codinghead/touchshield/documentation/SPI-transfer-1.png

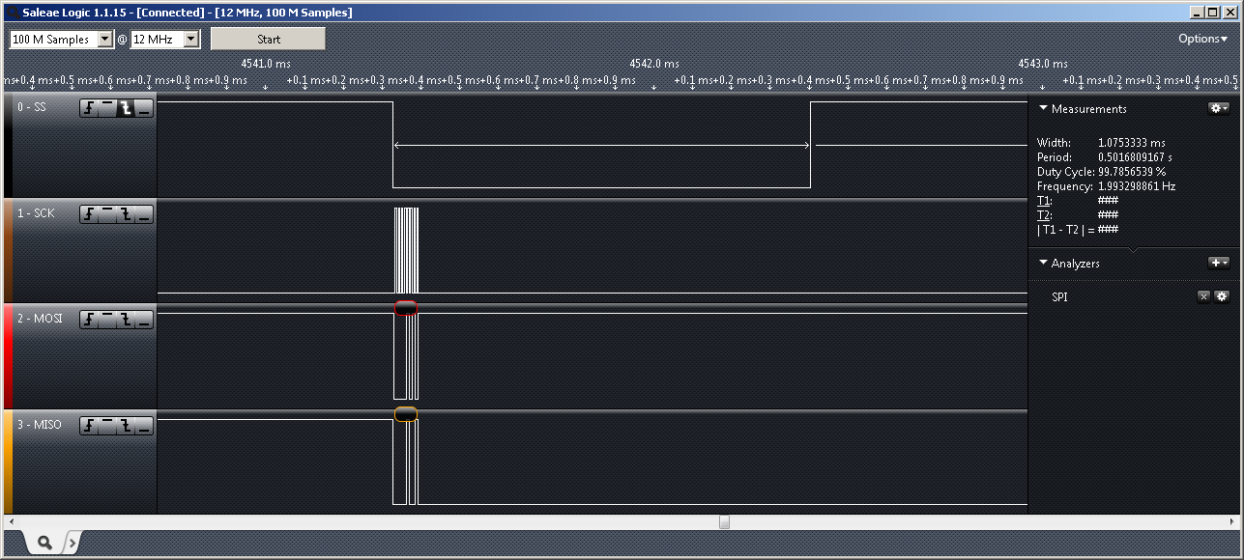
documentation/SPI-transfer-1.png
