codinghead/touchshield/documentation/SPI-transfer-2.png

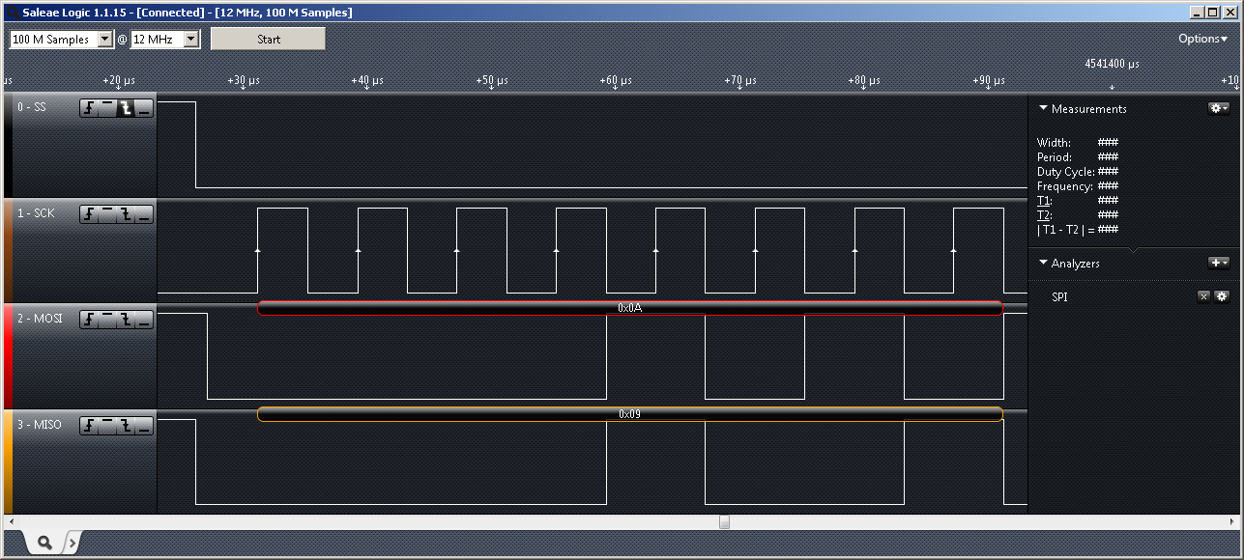
documentation/SPI-transfer-2.png
