codinghead/touchshield/documentation/SPI-transfer-3-SS-Rises-Too-Early.png

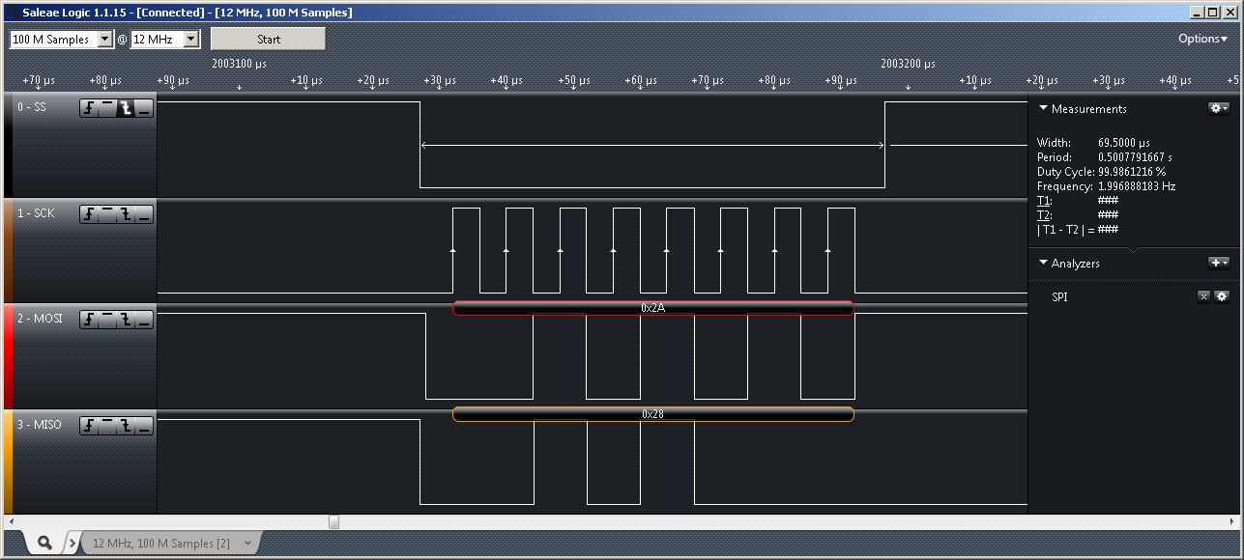
documentation/SPI-transfer-3-SS-Rises-Too-Early.png
