codinghead/touchshield/documentation/SPI-transfer-4-SS-Rises-Too-Early.png

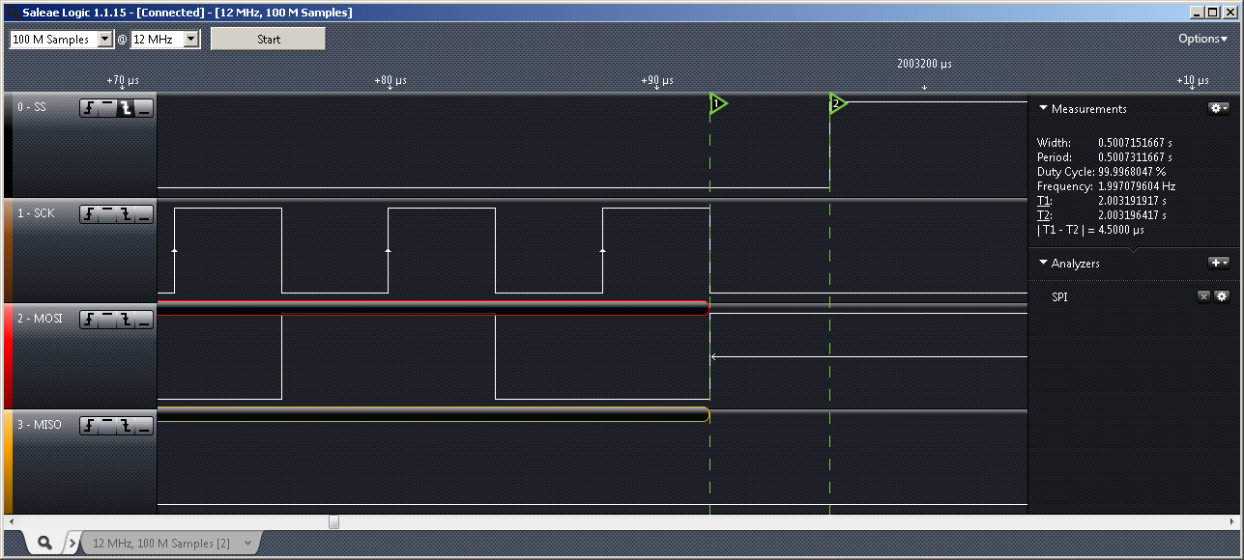
documentation/SPI-transfer-4-SS-Rises-Too-Early.png
