codinghead/touchshield/documentation/SPI-transfer-5-5-byte-packets-full-speed.png

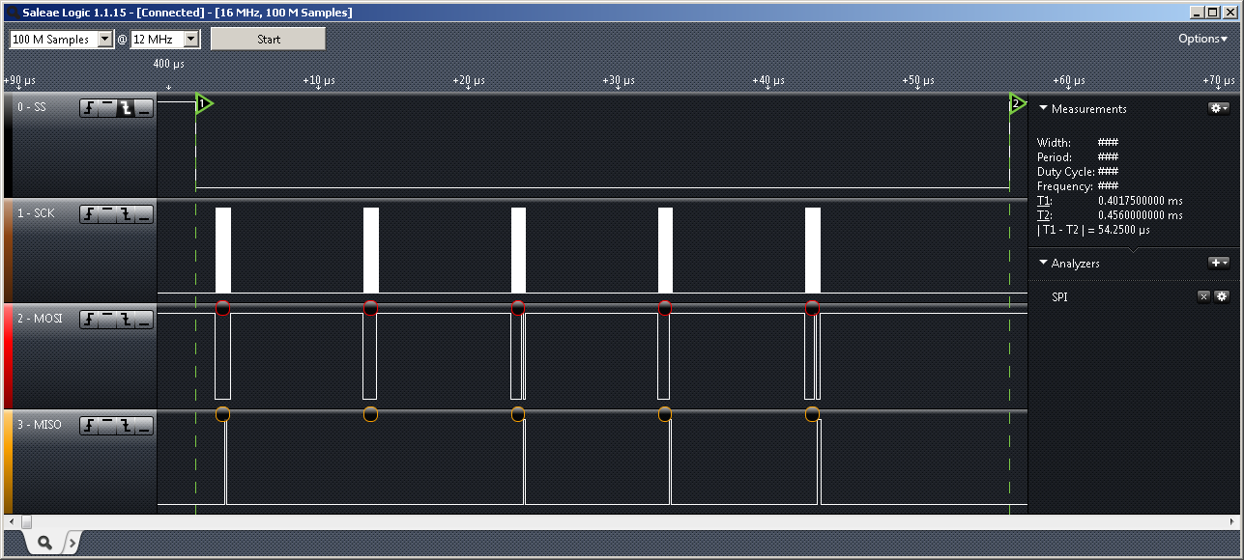
documentation/SPI-transfer-5-5-byte-packets-full-speed.png
