codinghead/touchshield/documentation/SPI-transfer-6-5-byte-packets-first-transfer.png

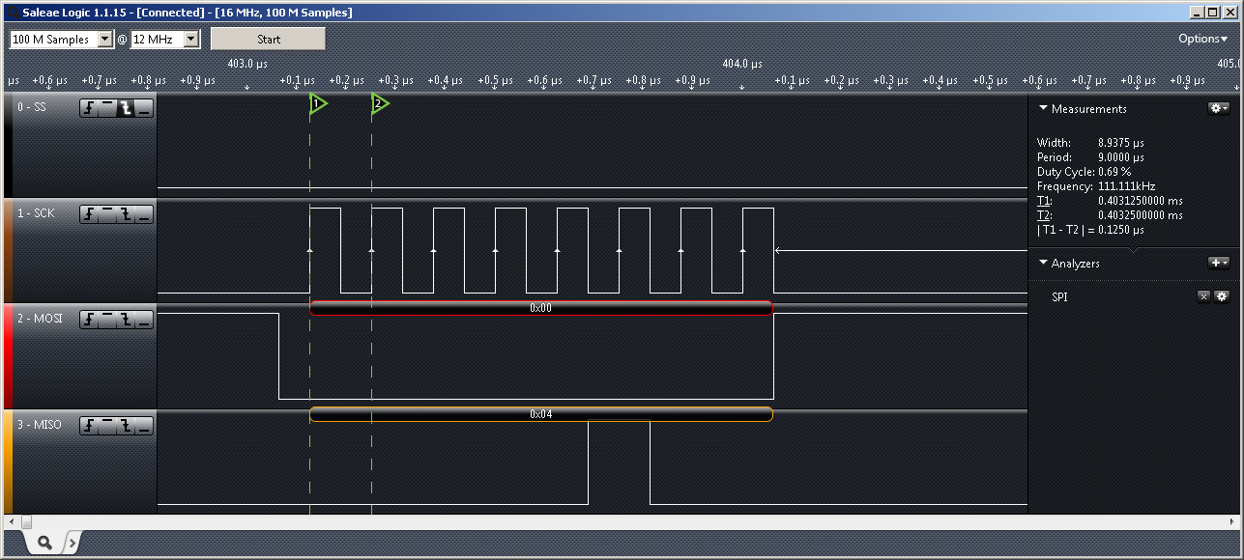
documentation/SPI-transfer-6-5-byte-packets-first-transfer.png
