codinghead/touchshield/documentation/SPI-transfer-7-5-byte-packets-SS-fall-edge-to-first-CLK.png

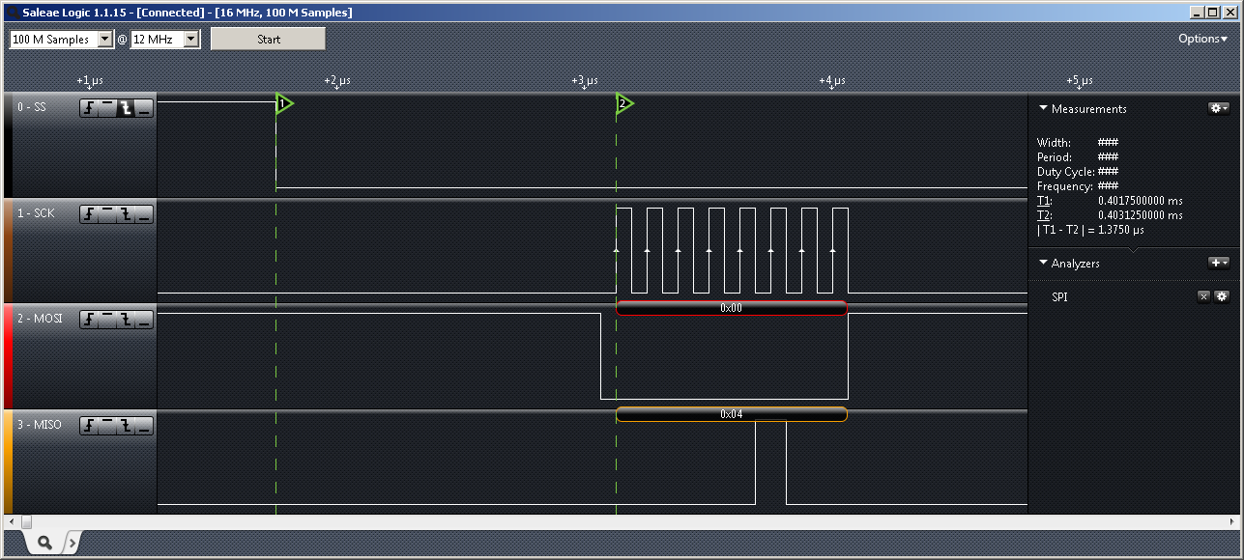
documentation/SPI-transfer-7-5-byte-packets-SS-fall-edge-to-first-CLK.png
