codinghead/touchshield/documentation/SPI-transfer-8-5-byte-packets-last-CLK-to-SS-rising-edge.png

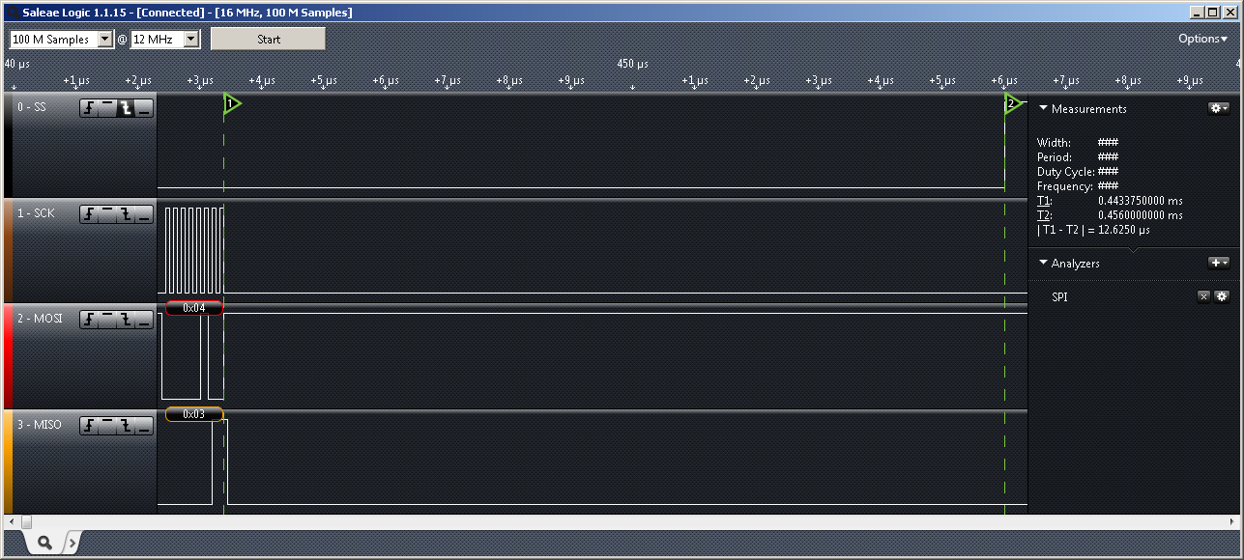
documentation/SPI-transfer-8-5-byte-packets-last-CLK-to-SS-rising-edge.png
