codinghead/touchshield/images/by-sa.bmp

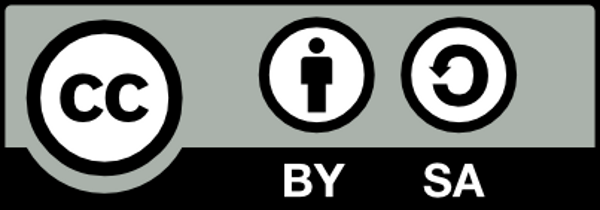
images/by-sa.bmp
