codinghead/touchshield/images/MultiTouch-Interface_Mouse-theme_1-finger-Simple-Tap.png

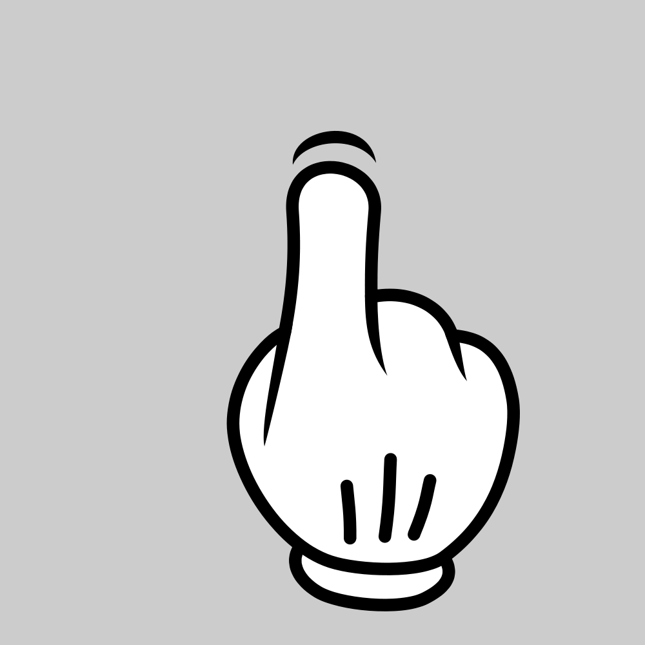
images/MultiTouch-Interface_Mouse-theme_1-finger-Simple-Tap.png
