codinghead/touchshield/images/QTouchShieldRender2.png

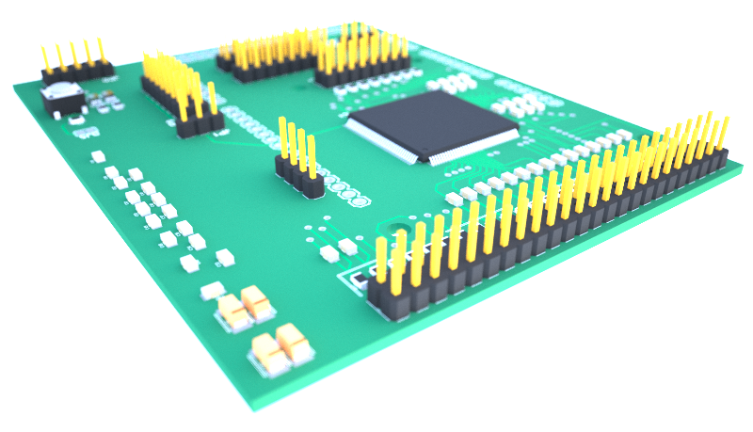
images/QTouchShieldRender2.png
