codinghead/touchshield/software/uc3c0512c/UC3C-Test/UC3C-Test/src/config/conf_board.h

/**
 * \file
 *
 * \brief User board configuration template
 *
 */

#ifndef CONF_BOARD_H
#define CONF_BOARD_H

// External oscillator settings.
// Uncomment and set correct values if external oscillator is used.

// External oscillator frequency
//#define BOARD_XOSC_HZ          8000000

// External oscillator type.
//!< External clock signal
//#define BOARD_XOSC_TYPE        XOSC_TYPE_EXTERNAL
//!< 32.768 kHz resonator on TOSC
//#define BOARD_XOSC_TYPE        XOSC_TYPE_32KHZ
//!< 0.4 to 16 MHz resonator on XTALS
//#define BOARD_XOSC_TYPE        XOSC_TYPE_XTAL

// External oscillator startup time
//#define BOARD_XOSC_STARTUP_US  500000

// Define SPI0 interface on PORTD
#define SPI0_SS         AVR32_PIN_PD03
#define SPI0_MOSI       AVR32_PIN_PD04
#define SPI0_MISO       AVR32_PIN_PD05
#define SPI0_SCK        AVR32_PIN_PD06

#endif // CONF_BOARD_H
