codinghead/touchshield/software/uc3c0512c/UC3C-Test/UC3C-Test/src/asf/avr32/drivers/scif/scif_uc3c.c

/*****************************************************************************
 *
 * \file
 *
 * \brief System Control InterFace(SCIF) driver.
 *
 * Copyright (c) 2009 Atmel Corporation. All rights reserved.
 *
 * \asf_license_start
 *
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
 * 3. The name of Atmel may not be used to endorse or promote products derived
 *    from this software without specific prior written permission.
 *
 * 4. This software may only be redistributed and used in connection with an
 *    Atmel microcontroller product.
 *
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
 * \asf_license_stop
 *
 *****************************************************************************/


#include "compiler.h"
#include "scif_uc3c.h"


/*! \name SCIF Writable Bit-Field Registers
 */
//! @{

typedef union
{
  unsigned long                 oscctrl[2];
  avr32_scif_oscctrl_t          OSCCTRL[2];
} u_avr32_scif_oscctrl_t;

typedef union
{
  unsigned long                 pll[2];
  avr32_scif_pll_t              PLL[2];
} u_avr32_scif_pll_t;

typedef union
{
  unsigned long                 oscctrl32;
  avr32_scif_oscctrl32_t         OSCCTRL32;
} u_avr32_scif_oscctrl32_t;



//! @}


//----- PRIVATE FUNCTIONS

/*! \brief Wait for a status high in the Power and Clocks status register.
 *
 * \param statusMask Mask field of the status to poll [INPUT]
 *
 * \return Status.
 *   \retval 0   Status is high.
 *   \retval <0  SCIF_POLL_TIMEOUT Timeout expired before the status was high.
 */
static long int scif_pclksr_statushigh_wait(unsigned long statusMask)
{
  unsigned int  timeout = SCIF_POLL_TIMEOUT;

  while(!(AVR32_SCIF.pclksr & statusMask))
  {
    if(--timeout == 0)
      return -1;
  }
  return PASS;
}

unsigned long scif_read_gplp(unsigned long gplp)
{
  return AVR32_SCIF.gplp[gplp];
}


void scif_write_gplp(int gplp, unsigned long value)
{
  SCIF_UNLOCK(AVR32_SCIF_GPLP + 4*gplp);
  AVR32_SCIF.gplp[gplp] = value;
}

/**
 ** Interrupt Functions
 **/
// Implemented as inline in scif_uc3x.h


/**
 ** Power and Clocks Status Functions
 **/
// Implemented as inline in scif_uc3x.h


/**
 ** OSC0/OSC1 Functions
 **/

long int scif_start_osc(scif_osc_t osc, const scif_osc_opt_t *opt, bool wait_for_ready)
{
  u_avr32_scif_oscctrl_t   u_avr32_scif_oscctrl;

#ifdef AVR32SFW_INPUT_CHECK
  // Check that the input frequency is in the supported frequency range.
  if( (opt->freq_hz < SCIF_EXT_CRYSTAL_MIN_FREQ_HZ)
      || (opt->freq_hz > SCIF_EXT_CRYSTAL_MAX_FREQ_HZ))
  {
    return -1;
  }
  // Check : for OSC0/OSC1, only 2 modes are supported
  if( (opt->mode != SCIF_OSC_MODE_EXT_CLK)
      && (opt->mode != SCIF_OSC_MODE_2PIN_CRYSTAL))
  {
    return -1;
  }

  if (osc == SCIF_OSC0)
  {
    // Check that the startup value is in the supported range.
    if(opt->startup > (unsigned char)AVR32_SCIF_OSCCTRL0_STARTUP_16384_RCOSC)
    {
      return -1;
    }
    // Check that the gain value is in the supported range.
    if(opt->gain > AVR32_SCIF_OSCCTRL0_GAIN_G3)
    {
      return -1;
    }
  }
  else
  {
    // Check that the startup value is in the supported range.
    if(opt->startup > (unsigned char)AVR32_SCIF_OSCCTRL1_STARTUP_16384_RCOSC)
    {
      return -1;
    }
    // Check that the gain value is in the supported range.
    if(opt->gain > AVR32_SCIF_OSCCTRL1_GAIN_G3)
    {
      return -1;
    }
  }
#endif  // AVR32SFW_INPUT_CHECK
  // Read Register
  u_avr32_scif_oscctrl.OSCCTRL[osc] = AVR32_SCIF.OSCCTRL[osc] ;
  // Modify: Configure & start OSC0.
  u_avr32_scif_oscctrl.OSCCTRL[osc].mode = opt->mode;
  u_avr32_scif_oscctrl.OSCCTRL[osc].gain = opt->gain;
  u_avr32_scif_oscctrl.OSCCTRL[osc].startup = opt->startup;
  u_avr32_scif_oscctrl.OSCCTRL[osc].oscen = ENABLE;
  AVR32_ENTER_CRITICAL_REGION( );
  // Unlock the write-protected OSCCTRL0 register
  SCIF_UNLOCK(AVR32_SCIF_OSCCTRL + 4*osc);
  // Write Back
  AVR32_SCIF.OSCCTRL[osc] = u_avr32_scif_oscctrl.OSCCTRL[osc];
  AVR32_LEAVE_CRITICAL_REGION( );

  if(true == wait_for_ready)
  {
    // Wait until OSC0 is stable and ready to be used.
    if(scif_pclksr_statushigh_wait(AVR32_SCIF_PCLKSR_OSC0RDY_MASK))
      return -1;
  }
  return PASS;
}


bool scif_is_osc_ready(scif_osc_t osc)
{
  if (osc == SCIF_OSC0)
  {
    return((AVR32_SCIF.pclksr & AVR32_SCIF_PCLKSR_OSC0RDY_MASK)>>AVR32_SCIF_PCLKSR_OSC0RDY_OFFSET);
  }
  else
  {
    return((AVR32_SCIF.pclksr & AVR32_SCIF_PCLKSR_OSC1RDY_MASK)>>AVR32_SCIF_PCLKSR_OSC1RDY_OFFSET);
  }
}


long int scif_stop_osc(scif_osc_t osc)
{

  unsigned long temp;

  temp = AVR32_SCIF.oscctrl[osc];
  temp &= ~AVR32_SCIF_OSCCTRL_OSCEN_MASK;
  AVR32_ENTER_CRITICAL_REGION( );
  // Unlock the write-protected OSCCTRL0 register
  SCIF_UNLOCK(AVR32_SCIF_OSCCTRL + 4*osc);
  // Stop OSC0.
  AVR32_SCIF.oscctrl[osc] = temp;
  AVR32_LEAVE_CRITICAL_REGION( );

  return PASS;
}


long int scif_configure_osc_crystalmode(scif_osc_t osc, unsigned int fcrystal)
{
  u_avr32_scif_oscctrl_t   u_avr32_scif_oscctrl;

  if (osc == SCIF_OSC0)
  {
    // Read Register
    u_avr32_scif_oscctrl.OSCCTRL[SCIF_OSC0] = AVR32_SCIF.OSCCTRL[SCIF_OSC0] ;
    // Modify : Configure the oscillator mode to crystal and set the gain according to the
    // cyrstal frequency.
    u_avr32_scif_oscctrl.OSCCTRL[SCIF_OSC0].mode = SCIF_OSC_MODE_2PIN_CRYSTAL;
    u_avr32_scif_oscctrl.OSCCTRL[SCIF_OSC0].gain = (fcrystal <  900000) ? AVR32_SCIF_OSCCTRL0_GAIN_G0 :
                                                   (fcrystal < 3000000) ? AVR32_SCIF_OSCCTRL0_GAIN_G1 :
                                                   (fcrystal < 8000000) ? AVR32_SCIF_OSCCTRL0_GAIN_G2 :
                                                                          AVR32_SCIF_OSCCTRL0_GAIN_G3;
    AVR32_ENTER_CRITICAL_REGION( );
    // Unlock the write-protected OSCCTRL0 register
    SCIF_UNLOCK(AVR32_SCIF_OSCCTRL);
    // Write Back
    AVR32_SCIF.OSCCTRL[SCIF_OSC0] = u_avr32_scif_oscctrl.OSCCTRL[SCIF_OSC0];
    AVR32_LEAVE_CRITICAL_REGION( );
  }
  else
  {
    // Read Register
    u_avr32_scif_oscctrl.OSCCTRL[SCIF_OSC1] = AVR32_SCIF.OSCCTRL[SCIF_OSC1] ;
    // Modify : Configure the oscillator mode to crystal and set the gain according to the
    // cyrstal frequency.
    u_avr32_scif_oscctrl.OSCCTRL[SCIF_OSC1].mode = SCIF_OSC_MODE_2PIN_CRYSTAL;
    u_avr32_scif_oscctrl.OSCCTRL[SCIF_OSC1].gain = (fcrystal <  900000) ? AVR32_SCIF_OSCCTRL1_GAIN_G0 :
                                                   (fcrystal < 3000000) ? AVR32_SCIF_OSCCTRL1_GAIN_G1 :
                                                   (fcrystal < 8000000) ? AVR32_SCIF_OSCCTRL1_GAIN_G2 :
                                                                          AVR32_SCIF_OSCCTRL1_GAIN_G3;
    AVR32_ENTER_CRITICAL_REGION( );
    // Unlock the write-protected OSCCTRL1 register
    SCIF_UNLOCK(AVR32_SCIF_OSCCTRL + 4);
    // Write Back
    AVR32_SCIF.OSCCTRL[SCIF_OSC1] = u_avr32_scif_oscctrl.OSCCTRL[SCIF_OSC1];
    AVR32_LEAVE_CRITICAL_REGION( );
  }

  return PASS;
}

long int scif_configure_osc_extmode(scif_osc_t osc)
{
  u_avr32_scif_oscctrl_t   u_avr32_scif_oscctrl;

      // Read Register
    u_avr32_scif_oscctrl.OSCCTRL[osc] = AVR32_SCIF.OSCCTRL[osc] ;
    // Modify : Configure the oscillator mode to crystal and set the gain according to the
    // cyrstal frequency.
    u_avr32_scif_oscctrl.OSCCTRL[osc].mode = SCIF_OSC_MODE_EXT_CLK;
    AVR32_ENTER_CRITICAL_REGION( );
    // Unlock the write-protected OSCCTRL0 register
    SCIF_UNLOCK(AVR32_SCIF_OSCCTRL + 4*osc);
    // Write Back
    AVR32_SCIF.OSCCTRL[osc] = u_avr32_scif_oscctrl.OSCCTRL[osc];
    AVR32_LEAVE_CRITICAL_REGION( );

  return PASS;
}

long int scif_enable_osc(scif_osc_t osc, unsigned int startup, bool wait_for_ready)
{

  u_avr32_scif_oscctrl_t   u_avr32_scif_oscctrl;

  // Read Register
  u_avr32_scif_oscctrl.OSCCTRL[osc] = AVR32_SCIF.OSCCTRL[osc] ;
  // Modify: Configure the oscillator startup and enable the osc.
  u_avr32_scif_oscctrl.OSCCTRL[osc].startup = startup;
  u_avr32_scif_oscctrl.OSCCTRL[osc].oscen = ENABLE;
  AVR32_ENTER_CRITICAL_REGION( );
  // Unlock the write-protected OSCCTRL0 register
  SCIF_UNLOCK(AVR32_SCIF_OSCCTRL + 4*osc);
  // Write Back
  AVR32_SCIF.OSCCTRL[osc] = u_avr32_scif_oscctrl.OSCCTRL[osc];
  AVR32_LEAVE_CRITICAL_REGION( );

  if(true == wait_for_ready)
  {
    // Wait until OSC0 is stable and ready to be used.
    if(scif_pclksr_statushigh_wait(AVR32_SCIF_PCLKSR_OSC0RDY_MASK))
      return -1;
  }

  return PASS;
}

long int scif_enable_extosc(scif_osc_t osc)
{

  u_avr32_scif_oscctrl_t   u_avr32_scif_oscctrl;

  // Read Register
  u_avr32_scif_oscctrl.OSCCTRL[osc] = AVR32_SCIF.OSCCTRL[osc] ;
  // Modify : Enable the osc.
  u_avr32_scif_oscctrl.OSCCTRL[osc].oscen = ENABLE;
  AVR32_ENTER_CRITICAL_REGION( );
  // Unlock the write-protected OSCCTRL0 register
  SCIF_UNLOCK(AVR32_SCIF_OSCCTRL + 4*osc);
  // Write Back
  AVR32_SCIF.OSCCTRL[osc] = u_avr32_scif_oscctrl.OSCCTRL[osc];
  AVR32_LEAVE_CRITICAL_REGION( );

  return PASS;
}

/**
 ** PLL0/PLL1 Functions
 **/
long int scif_pll_setup(scif_pll_t pll, const scif_pll_opt_t opt)
{

  u_avr32_scif_pll_t   u_avr32_scif_pll;

  // Read Register
  u_avr32_scif_pll.PLL[pll] = AVR32_SCIF.PLL[pll] ;
  // Modify Configuration
  u_avr32_scif_pll.PLL[pll].pllosc  = opt.osc;
  u_avr32_scif_pll.PLL[pll].pllopt  = opt.pll_freq | (opt.pll_div2 << 1) | (opt.pll_wbwdisable << 2);
  u_avr32_scif_pll.PLL[pll].plldiv   = opt.div;
  u_avr32_scif_pll.PLL[pll].pllmul  = opt.mul;
  u_avr32_scif_pll.PLL[pll].pllcount= opt.lockcount;
  AVR32_ENTER_CRITICAL_REGION( );
  // Unlock the write-protected PLL0 register
  SCIF_UNLOCK(AVR32_SCIF_PLL + 4*pll);
  // Write Back
  AVR32_SCIF.PLL[pll] = u_avr32_scif_pll.PLL[pll];
  AVR32_LEAVE_CRITICAL_REGION( );

  return PASS;
}

long int scif_pll_enable(scif_pll_t pll)
{

  u_avr32_scif_pll_t   u_avr32_scif_pll;

    // Read Register
    u_avr32_scif_pll.PLL[pll] = AVR32_SCIF.PLL[pll] ;
    // Modify Configuration
    u_avr32_scif_pll.PLL[pll].pllen = ENABLE;
    AVR32_ENTER_CRITICAL_REGION( );
    // Unlock the write-protected PLL0 register
    SCIF_UNLOCK(AVR32_SCIF_PLL + 4*pll);
    // Write Back
    AVR32_SCIF.PLL[pll] = u_avr32_scif_pll.PLL[pll];
    AVR32_LEAVE_CRITICAL_REGION( );

  return PASS;
}

long int scif_pll_disable(scif_pll_t pll)
{

  u_avr32_scif_pll_t   u_avr32_scif_pll;

  // Read Register
  u_avr32_scif_pll.PLL[pll] = AVR32_SCIF.PLL[pll] ;
  // Modify Configuration
  u_avr32_scif_pll.PLL[pll].pllen = DISABLE;
  AVR32_ENTER_CRITICAL_REGION( );
  // Unlock the write-protected PLL0 register
  SCIF_UNLOCK(AVR32_SCIF_PLL + 4*pll);
  // Write Back
  AVR32_SCIF.PLL[pll] = u_avr32_scif_pll.PLL[pll];
  AVR32_LEAVE_CRITICAL_REGION( );

  return PASS;
}

long int scif_wait_for_pll_locked(scif_pll_t pll)
{

  if (pll == SCIF_PLL0)
  {
      // Wait until PLL0 is stable and ready to be used.
      while(!(AVR32_SCIF.pclksr & AVR32_SCIF_PCLKSR_PLL0_LOCK_MASK));
  }
  else
  {
      // Wait until PLL1 is stable and ready to be used.
      while(!(AVR32_SCIF.pclksr & AVR32_SCIF_PCLKSR_PLL1_LOCK_MASK));
  }

  return PASS;
}

/**
 ** OSC32 Functions
 **/

long int scif_start_osc32(const scif_osc32_opt_t *opt, bool wait_for_ready)
{
  u_avr32_scif_oscctrl32_t  u_avr32_scif_oscctrl32;


#ifdef AVR32SFW_INPUT_CHECK
  // Check that the input frequency is in the supported frequency range.
  if( (opt->freq_hz < SCIF_EXT_CRYSTAL_MIN_FREQ_HZ)
      || (opt->freq_hz > SCIF_EXT_CRYSTAL_MAX_FREQ_HZ))
  {
    return -1;
  }
  // Check : for OSC0/OSC1, only 2 modes are supported
  if( (opt->mode < SCIF_OSC_MODE_EXT_CLK)
      || (opt->mode > SCIF_OSC_MODE_2PIN_CRYSTAL)
      || (opt->mode == SCIF_OSC_MODE_NOT_SUPPORTED_1)
      || (opt->mode == SCIF_OSC_MODE_NOT_SUPPORTED_2) )
  {
    return -1;
  }
  // Check that the startup value is in the supported range.
  if(opt->startup > (unsigned char)AVR32_SCIF_OSCCTRL32_STARTUP_524288_RCOSC)
  {
    return -1;
  }
#endif  // AVR32SFW_INPUT_CHECK

  // Read Register
  u_avr32_scif_oscctrl32.oscctrl32 = AVR32_SCIF.oscctrl32 ;

  // Modify : Configure & start OSC32.
  u_avr32_scif_oscctrl32.OSCCTRL32.mode = opt->mode;
  u_avr32_scif_oscctrl32.OSCCTRL32.startup = opt->startup;
  u_avr32_scif_oscctrl32.OSCCTRL32.osc32en = ENABLE;

  AVR32_ENTER_CRITICAL_REGION( );
  // Unlock the write-protected OSCCTRL32 register
  SCIF_UNLOCK(AVR32_SCIF_OSCCTRL32);

  // Write Back
  AVR32_SCIF.oscctrl32 = u_avr32_scif_oscctrl32.oscctrl32;
  AVR32_LEAVE_CRITICAL_REGION( );

  if(true == wait_for_ready)
  {
    // Wait until OSC32 is stable and ready to be used.
    if(scif_pclksr_statushigh_wait(AVR32_SCIF_PCLKSR_OSC32RDY_MASK))
      return -1;
  }

  return PASS;
}


long scif_stop_osc32()
{
  unsigned long temp = AVR32_SCIF.oscctrl32;
  temp &= ~AVR32_SCIF_OSCCTRL32_OSC32EN_MASK;

  AVR32_ENTER_CRITICAL_REGION( );
  // Unlock the write-protected OSCCTRL32 register
  SCIF_UNLOCK(AVR32_SCIF_OSCCTRL32);

  // Stop OSC32.
  AVR32_SCIF.oscctrl32 = temp;
  AVR32_LEAVE_CRITICAL_REGION( );

  return PASS;
}


/**
 ** Calibration Functions
 **/


/**
 ** Critical Path Oscillator Functions
 **/

/**
 ** 8MHz RCosc Functions
 **/

void scif_start_rc8M(void)
{
  unsigned int* calibration_bits = (unsigned int*)0x80800200;
  AVR32_ENTER_CRITICAL_REGION( );
  // Unlock the write-protected RC8MCR register
  SCIF_UNLOCK(AVR32_SCIF_RCCR8);
  AVR32_SCIF.rccr8 = AVR32_SCIF_RCCR8_RCOSC8_EN_MASK | ((*calibration_bits)&AVR32_SCIF_RCCR8_CALIB_MASK);
  AVR32_LEAVE_CRITICAL_REGION( );
}

void scif_stop_rc8M(void)
{
  unsigned long temp = AVR32_SCIF.rccr8;

  AVR32_ENTER_CRITICAL_REGION( );
  // Unlock the write-protected RC8MCR register
  SCIF_UNLOCK(AVR32_SCIF_RCCR8);
  temp &= ~AVR32_SCIF_RCCR8_RCOSC8_EN_MASK;
  AVR32_SCIF.rccr8 = temp;
  AVR32_LEAVE_CRITICAL_REGION( );
}

/**
 ** 120MHz RCosc Functions
 **/

void scif_start_rc120M(void)
{
  AVR32_ENTER_CRITICAL_REGION( );
  // Unlock the write-protected RC120MCR register
  SCIF_UNLOCK(AVR32_SCIF_RC120MCR);
  AVR32_SCIF.rc120mcr = AVR32_SCIF_RC120MCR_EN_MASK;
  AVR32_LEAVE_CRITICAL_REGION( );
}

void scif_stop_rc120M(void)
{
  unsigned long temp = AVR32_SCIF.rc120mcr;

  AVR32_ENTER_CRITICAL_REGION( );
  // Unlock the write-protected RC120MCR register
  SCIF_UNLOCK(AVR32_SCIF_RC120MCR);
  temp &= ~AVR32_SCIF_RC120MCR_EN_MASK;
  AVR32_SCIF.rc120mcr = temp;
  AVR32_LEAVE_CRITICAL_REGION( );
}



/**
 ** Generic Clock Functions
 **/

long int scif_start_gclk(unsigned int gclk, const scif_gclk_opt_t *opt)
{
#ifdef AVR32SFW_INPUT_CHECK
  // Check that the generic clock number is correct
  if( gclk > AVR32_SCIF_GCLK_NUM )
  {
    return -1;
  }
  // Check that the clock source for the generic clock is correct.
  if(( opt->clock_source >= SCIF_GCCTRL_OSCSEL_INVALID ) || ( opt->clock_source < 0 ))
  {
    return -1;
  }
#endif  // AVR32SFW_INPUT_CHECK

  // If the generic clock is already enabled, return an error.
  if(AVR32_SCIF.gcctrl[gclk] & AVR32_SCIF_GCCTRL_CEN_MASK)
    return -1;

  // Configure & start the generic clock.
  AVR32_SCIF.gcctrl[gclk] = ((opt->divider << AVR32_SCIF_GCCTRL_DIV_OFFSET)&AVR32_SCIF_GCCTRL_DIV_MASK)
                            |((opt->diven << AVR32_SCIF_GCCTRL_DIVEN_OFFSET)&AVR32_SCIF_GCCTRL_DIVEN_MASK)
                            |((opt->clock_source << AVR32_SCIF_GCCTRL_OSCSEL_OFFSET)&AVR32_SCIF_GCCTRL_OSCSEL_MASK)
                            |(AVR32_SCIF_GCCTRL_CEN_MASK);

  return PASS;
}


long int scif_stop_gclk(unsigned int gclk)
{
  unsigned int  timeout = SCIF_POLL_TIMEOUT;

#ifdef AVR32SFW_INPUT_CHECK
  // Check that the generic clock number is correct
  if( gclk > AVR32_SCIF_GCLK_NUM )
  {
    return -1;
  }
#endif  // AVR32SFW_INPUT_CHECK

  // Stop the generic clock.
  AVR32_SCIF.gcctrl[gclk] &= ~AVR32_SCIF_GCCTRL_CEN_MASK;

  // Wait until the generic clock is actually stopped.
  while(AVR32_SCIF.gcctrl[gclk] & AVR32_SCIF_GCCTRL_CEN_MASK)
  {
    if(--timeout == 0)
      return -1;
  }

  return PASS;
}


long int scif_gc_setup(unsigned int gclk, scif_gcctrl_oscsel_t clk_src, unsigned int diven, unsigned int divfactor)
{
  int restart_gc = false;


  // Change the division factor to conform to the equation: fgclk = fsrc/divfactor = fsrc/(2*(div+1))
  divfactor = (divfactor>>1) -1;

#ifdef AVR32SFW_INPUT_CHECK
  // Check that the generic clock number is correct
  if( gclk > AVR32_SCIF_GCLK_NUM )
  {
    return -1;
  }
  // Check that the clock source for the generic clock is correct.
  if(( clk_src >= SCIF_GCCTRL_OSCSEL_INVALID ) || ( clk_src < 0 ))
  {
    return -1;
  }
  // Check that the required division factor is correct.
  if(diven)
  {
    if(divfactor >= (1<<AVR32_SCIF_GCCTRL_DIV_SIZE))
      return -1;
  }
#endif  // AVR32SFW_INPUT_CHECK

  // If the generic clock is already enabled, disable it before changing its setup.
  if(AVR32_SCIF.gcctrl[gclk] & AVR32_SCIF_GCCTRL_CEN_MASK)
  {
    restart_gc = true;
    if(scif_stop_gclk(gclk) < 0)
      return -1;  // Could not stop the generic clock.
  }

  // Setup the generic clock.
  AVR32_SCIF.gcctrl[gclk] = ((divfactor << AVR32_SCIF_GCCTRL_DIV_OFFSET)&AVR32_SCIF_GCCTRL_DIV_MASK)
                            |((diven << AVR32_SCIF_GCCTRL_DIVEN_OFFSET)&AVR32_SCIF_GCCTRL_DIVEN_MASK)
                            |((clk_src << AVR32_SCIF_GCCTRL_OSCSEL_OFFSET)&AVR32_SCIF_GCCTRL_OSCSEL_MASK);

  // Restart the gc if it previously was enabled.
  if(true == restart_gc)
    AVR32_SCIF.gcctrl[gclk] |= AVR32_SCIF_GCCTRL_CEN_MASK ;

  return PASS;
}


long int scif_gc_enable(unsigned int gclk)
{
#ifdef AVR32SFW_INPUT_CHECK
  // Check that the generic clock number is correct
  if( gclk > AVR32_SCIF_GCLK_NUM )
  {
    return -1;
  }
#endif  // AVR32SFW_INPUT_CHECK

  // If the generic clock is already enabled, do nothing.
  if(!(AVR32_SCIF.gcctrl[gclk] & AVR32_SCIF_GCCTRL_CEN_MASK))
    AVR32_SCIF.gcctrl[gclk] |= AVR32_SCIF_GCCTRL_CEN_MASK;

  return PASS;

}

void scif_bod18_enable_irq(void)
{
  AVR32_SCIF.ier = AVR32_SCIF_IER_BODDET_MASK ;
}

void scif_bod18_disable_irq(void)
{
  bool global_interrupt_enabled = Is_global_interrupt_enabled();

  if (global_interrupt_enabled) Disable_global_interrupt();
  AVR32_SCIF.idr = AVR32_SCIF_IDR_BODDET_MASK;
  AVR32_SCIF.isr;
  if (global_interrupt_enabled) Enable_global_interrupt();
}

void scif_bod18_clear_irq(void)
{
  AVR32_SCIF.icr = AVR32_SCIF_ICR_BODDET_MASK;
}

unsigned long scif_bod18_get_irq_status(void)
{
  return ((AVR32_SCIF.isr & AVR32_SCIF_ISR_BODDET_MASK) != 0);
}

unsigned long scif_bod18_get_irq_enable_bit(void)
{
  return ((AVR32_SCIF.imr & AVR32_SCIF_IMR_BODDET_MASK) != 0);
}

unsigned long scif_bod18_get_level(void)
{
  return (AVR32_SCIF.bod & AVR32_SCIF_BOD_LEVEL_MASK) >> AVR32_SCIF_BOD_LEVEL_OFFSET;
}

void scif_bod33_enable_irq(void)
{
  AVR32_SCIF.ier = AVR32_SCIF_IER_BOD33DET_MASK ;
}

void scif_bod33_disable_irq(void)
{
   bool global_interrupt_enabled = Is_global_interrupt_enabled();

  if (global_interrupt_enabled) Disable_global_interrupt();
  AVR32_SCIF.idr = AVR32_SCIF_IDR_BOD33DET_MASK;
  AVR32_SCIF.isr;
  if (global_interrupt_enabled) Enable_global_interrupt();
}

void scif_bod33_clear_irq(void)
{
  AVR32_SCIF.icr = AVR32_SCIF_ICR_BOD33DET_MASK;
}

unsigned long scif_bod33_get_irq_status(void)
{
  return ((AVR32_SCIF.isr & AVR32_SCIF_ISR_BOD33DET_MASK) != 0);
}

unsigned long scif_bod33_get_irq_enable_bit(void)
{
  return ((AVR32_SCIF.imr & AVR32_SCIF_IMR_BOD33DET_MASK) != 0);
}

unsigned long scif_bod33_get_level(void)
{
  return (AVR32_SCIF.bod33 & AVR32_SCIF_BOD33_LEVEL_MASK) >> AVR32_SCIF_BOD33_LEVEL_OFFSET;
}

void scif_bod50_enable_irq(void)
{
  AVR32_SCIF.ier = AVR32_SCIF_IER_BOD50DET_MASK ;
}

void scif_bod50_disable_irq(void)
{
   bool global_interrupt_enabled = Is_global_interrupt_enabled();

  if (global_interrupt_enabled) Disable_global_interrupt();
  AVR32_SCIF.idr = AVR32_SCIF_IDR_BOD50DET_MASK;
  AVR32_SCIF.isr;
  if (global_interrupt_enabled) Enable_global_interrupt();
}

void scif_bod50_clear_irq(void)
{
  AVR32_SCIF.icr = AVR32_SCIF_ICR_BOD50DET_MASK;
}

unsigned long scif_bod50_get_irq_status(void)
{
  return ((AVR32_SCIF.isr & AVR32_SCIF_ISR_BOD50DET_MASK) != 0);
}

unsigned long scif_bod50_get_irq_enable_bit(void)
{
  return ((AVR32_SCIF.imr & AVR32_SCIF_IMR_BOD50DET_MASK) != 0);
}

unsigned long scif_bod50_get_level(void)
{
  return (AVR32_SCIF.bod50 & AVR32_SCIF_BOD50_LEVEL_MASK) >> AVR32_SCIF_BOD50_LEVEL_OFFSET;
}
